Hubberthus/Arduino/cores/esp8266/spiffs_hal.cpp

/*
 spiffs_hal.cpp - SPI read/write/erase functions for SPIFFS.
 Copyright (c) 2015 Ivan Grokhotkov. All rights reserved.
 This file is part of the esp8266 core for Arduino environment.

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
 You should have received a copy of the GNU Lesser General Public
 License along with this library; if not, write to the Free Software
 Foundation, Inc., 51 Franklin St, Fifth Floor, Boston, MA  02110-1301  USA
 */

#include <Arduino.h>
#include <stdlib.h>
#include <algorithm>
#include "spiffs/spiffs.h"
#include "debug.h"

extern "C" {
#include "c_types.h"
#include "spi_flash.h"
}
/*
 spi_flash_read function requires flash address to be aligned on word boundary.
 We take care of this by reading first and last words separately and memcpy
 relevant bytes into result buffer.

alignment:       012301230123012301230123
bytes requested: -------***********------
read directly:   --------xxxxxxxx--------
read pre:        ----aaaa----------------
read post:       ----------------bbbb----
alignedBegin:            ^
alignedEnd:                      ^
*/

int32_t spiffs_hal_read(uint32_t addr, uint32_t size, uint8_t *dst) {
    optimistic_yield(10000);

    uint32_t result = SPIFFS_OK;
    uint32_t alignedBegin = (addr + 3) & (~3);
    uint32_t alignedEnd = (addr + size) & (~3);
    if (alignedEnd < alignedBegin) {
        alignedEnd = alignedBegin;
    }

    if (addr < alignedBegin) {
        uint32_t nb = alignedBegin - addr;
        uint32_t tmp;
        if (!ESP.flashRead(alignedBegin - 4, &tmp, 4)) {
            DEBUGV("_spif_read(%d) addr=%x size=%x ab=%x ae=%x\r\n",
                __LINE__, addr, size, alignedBegin, alignedEnd);
            return SPIFFS_ERR_INTERNAL;
        }
        memcpy(dst, &tmp + 4 - nb, nb);
    }

    if (alignedEnd != alignedBegin) {
        if (!ESP.flashRead(alignedBegin, (uint32_t*) (dst + alignedBegin - addr),
                alignedEnd - alignedBegin)) {
            DEBUGV("_spif_read(%d) addr=%x size=%x ab=%x ae=%x\r\n",
                __LINE__, addr, size, alignedBegin, alignedEnd);
            return SPIFFS_ERR_INTERNAL;
        }
    }

    if (addr + size > alignedEnd) {
        uint32_t nb = addr + size - alignedEnd;
        uint32_t tmp;
        if (!ESP.flashRead(alignedEnd, &tmp, 4)) {
            DEBUGV("_spif_read(%d) addr=%x size=%x ab=%x ae=%x\r\n",
                __LINE__, addr, size, alignedBegin, alignedEnd);
            return SPIFFS_ERR_INTERNAL;
        }

        memcpy(dst + size - nb, &tmp, nb);
    }

    return result;
}

/*
 Like spi_flash_read, spi_flash_write has a requirement for flash address to be
 aligned. However it also requires RAM address to be aligned as it reads data
 in 32-bit words. Flash address (mis-)alignment is handled much the same way
 as for reads, but for RAM alignment we have to copy data into a temporary
 buffer. The size of this buffer is a tradeoff between number of writes required
 and amount of stack required. This is chosen to be 512 bytes here, but might
 be adjusted in the future if there are good reasons to do so.
*/

static const int UNALIGNED_WRITE_BUFFER_SIZE = 512;

int32_t spiffs_hal_write(uint32_t addr, uint32_t size, uint8_t *src) {
    optimistic_yield(10000);

    uint32_t alignedBegin = (addr + 3) & (~3);
    uint32_t alignedEnd = (addr + size) & (~3);
    if (alignedEnd < alignedBegin) {
        alignedEnd = alignedBegin;
    }

    if (addr < alignedBegin) {
        uint32_t ofs = alignedBegin - addr;
        uint32_t nb = (size < ofs) ? size : ofs;
        uint8_t tmp[4] __attribute__((aligned(4))) = {0xff, 0xff, 0xff, 0xff};
        memcpy(tmp + 4 - ofs, src, nb);
        if (!ESP.flashWrite(alignedBegin - 4, (uint32_t*) tmp, 4)) {
            DEBUGV("_spif_write(%d) addr=%x size=%x ab=%x ae=%x\r\n",
                __LINE__, addr, size, alignedBegin, alignedEnd);
            return SPIFFS_ERR_INTERNAL;
        }
    }

    if (alignedEnd != alignedBegin) {
        uint32_t* srcLeftover = (uint32_t*) (src + alignedBegin - addr);
        uint32_t srcAlign = ((uint32_t) srcLeftover) & 3;
        if (!srcAlign) {
            if (!ESP.flashWrite(alignedBegin, (uint32_t*) srcLeftover,
                    alignedEnd - alignedBegin)) {
                DEBUGV("_spif_write(%d) addr=%x size=%x ab=%x ae=%x\r\n",
                    __LINE__, addr, size, alignedBegin, alignedEnd);
                return SPIFFS_ERR_INTERNAL;
            }
        }
        else {
            uint8_t buf[UNALIGNED_WRITE_BUFFER_SIZE];
            for (size_t sizeLeft = alignedEnd - alignedBegin; sizeLeft; ) {
                size_t willCopy = std::min(sizeLeft, sizeof(buf));
                memcpy(buf, srcLeftover, willCopy);

                if (!ESP.flashWrite(alignedBegin, (uint32_t*) buf, willCopy)) {
                    DEBUGV("_spif_write(%d) addr=%x size=%x ab=%x ae=%x\r\n",
                        __LINE__, addr, size, alignedBegin, alignedEnd);
                    return SPIFFS_ERR_INTERNAL;
                }

                sizeLeft -= willCopy;
                srcLeftover += willCopy;
                alignedBegin += willCopy;
            }
        }
    }

    if (addr + size > alignedEnd) {
        uint32_t nb = addr + size - alignedEnd;
        uint32_t tmp = 0xffffffff;
        memcpy(&tmp, src + size - nb, nb);

        if (!ESP.flashWrite(alignedEnd, &tmp, 4)) {
            DEBUGV("_spif_write(%d) addr=%x size=%x ab=%x ae=%x\r\n",
                __LINE__, addr, size, alignedBegin, alignedEnd);
            return SPIFFS_ERR_INTERNAL;
        }
    }

    return SPIFFS_OK;
}

int32_t spiffs_hal_erase(uint32_t addr, uint32_t size) {
    if ((size & (SPI_FLASH_SEC_SIZE - 1)) != 0 ||
        (addr & (SPI_FLASH_SEC_SIZE - 1)) != 0) {
        DEBUGV("_spif_erase called with addr=%x, size=%d\r\n", addr, size);
        abort();
    }
    const uint32_t sector = addr / SPI_FLASH_SEC_SIZE;
    const uint32_t sectorCount = size / SPI_FLASH_SEC_SIZE;
    for (uint32_t i = 0; i < sectorCount; ++i) {
        optimistic_yield(10000);
        if (!ESP.flashEraseSector(sector + i)) {
            DEBUGV("_spif_erase addr=%x size=%d i=%d\r\n", addr, size, i);
            return SPIFFS_ERR_INTERNAL;
        }
    }
    return SPIFFS_OK;
}
